InputBlackBoxOutput/Smart-Chessboard/code/connections.py

# AUX
AUX1  = 2  # I2C SDA
AUX2  = 3  # I2C SCL
AUX3  = 10 # SPI MOSI
AUX4  = 9  # SPI MISO
AUX5  = 11 # SPI CLK
AUX6  = 15 # UART TXD
AUX7  = 14 # UART RXD
AUX8  = 17
AUX9  = 27
AUX10 = 22

# Buzzer
BUZZ = 4

# Buttons
BTN1 = 6
BTN2 = 13
BTN3 = 19
BTN4 = 26

# Status LED
STAT_LED = 12

# Scan Demux
D_S0 = 16 
D_S1 = 20
D_S2 = 21

# Scan Mux
M_S0  = 25 
M_S1  = 8
M_S2  = 7
M_OUT = 24

# LED RGB Serial
LED_DATA = 18

#---------------------------------------------------------------------------------
